1h3rich/VirtualFriend/carcasa/previews/cuerpo_front.png

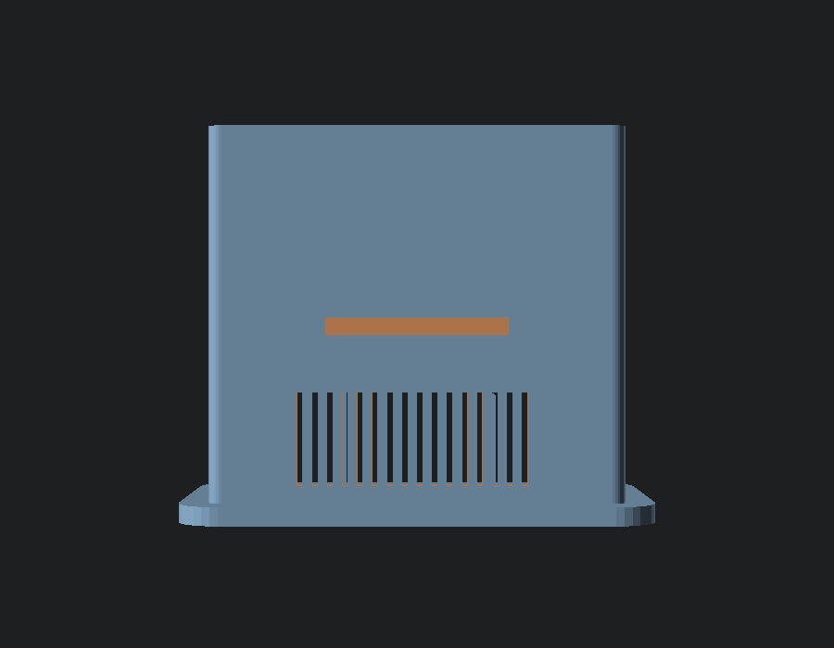
carcasa/previews/cuerpo_front.png
