1h3rich/VirtualFriend/carcasa/previews/cuerpo_right.png

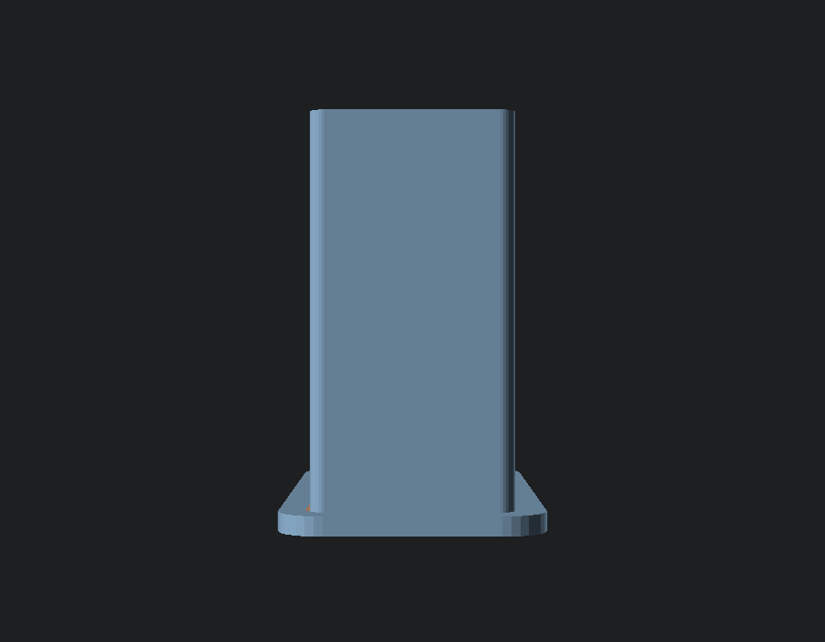
carcasa/previews/cuerpo_right.png
