1h3rich/VirtualFriend/carcasa/previews/virtualfriend_carcasa_back.png

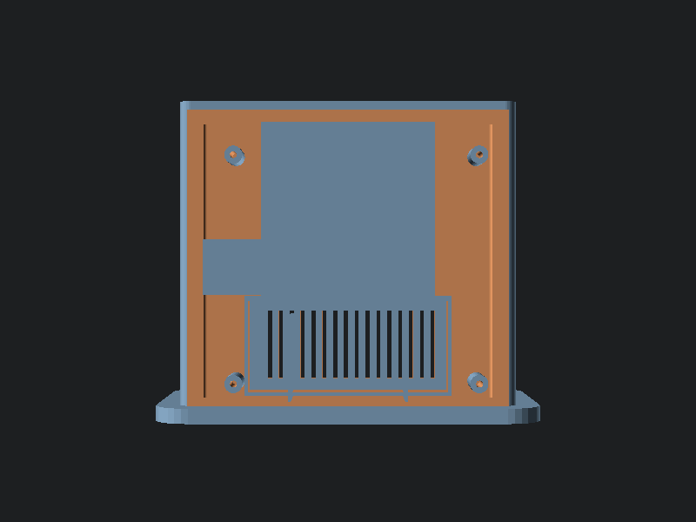
carcasa/previews/virtualfriend_carcasa_back.png
