1h3rich/VirtualFriend/carcasa/previews/virtualfriend_carcasa_screen_face.png

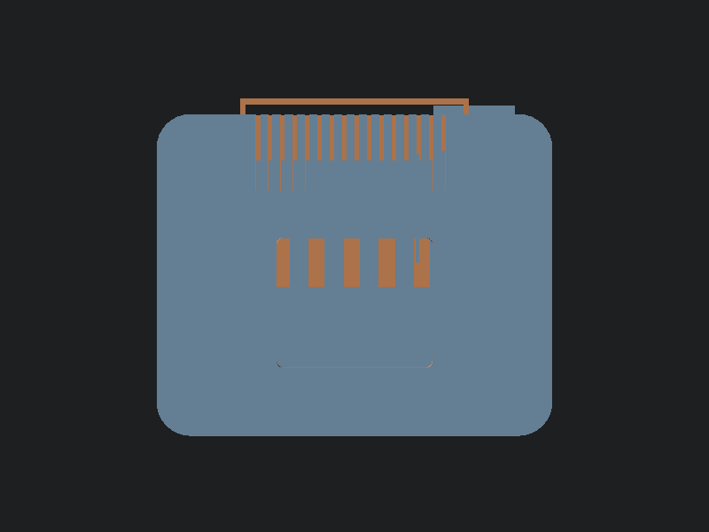
carcasa/previews/virtualfriend_carcasa_screen_face.png
