1h3rich/VirtualFriend/VirtualFriendInf/Diagramas/DiagramaDeCableado_v5.png

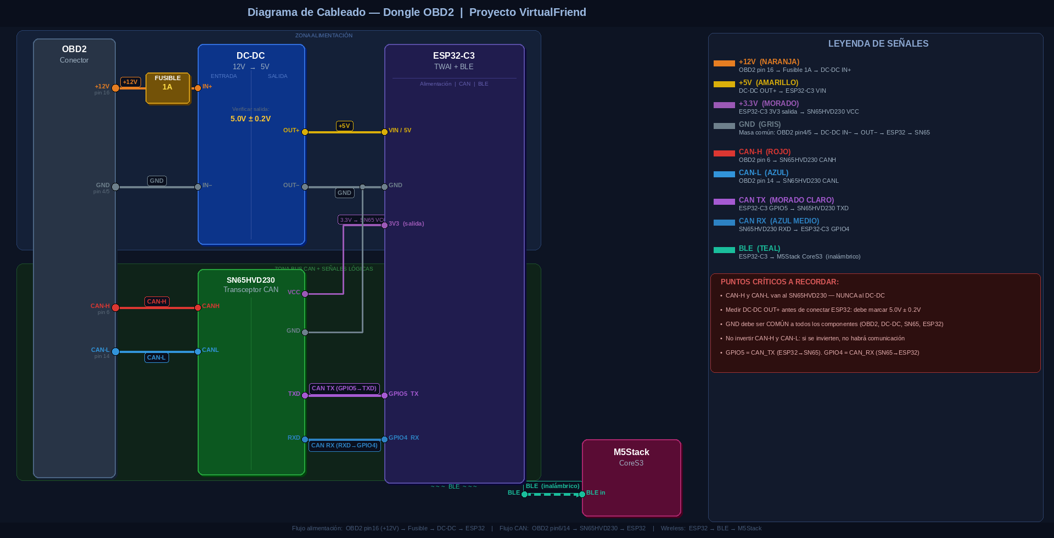
VirtualFriendInf/Diagramas/DiagramaDeCableado_v5.png
